alexnathanson/weathermachine/arduino-code/pumpDriver-Nov29-2022-PWM_DIR/pumpDriver-Nov29-2022-PWM_DIR.ino

/*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
 * This example shows how to drive a motor using the PWM and DIR pins.
 * This example only shows how to drive a single motor for simplicity.
 * For dual channel motor driver, both channel work the same way.
 * 
 * 
 * CONNECTIONS:
 * 
 * Arduino D3  - Motor Driver PWM Input
 * Arduino D4  - Motor Driver DIR Input
 * Arduino GND - Motor Driver GND
 *
 *
 * AUTHOR   : Kong Wai Weng
 * COMPANY  : Cytron Technologies Sdn Bhd
 * WEBSITE  : www.cytron.io
 * EMAIL    : support@cytron.io
 *
 *******************************************************************************/

 #include "CytronMotorDriver.h"


// Configure the motor driver.
CytronMD motor(PWM_DIR, 3, 4);  // PWM = Pin 3, DIR = Pin 4.


// The setup routine runs once when you press reset.
void setup() {
    motor.setSpeed(128);  // Run forward at 50% speed.

}


// The loop routine runs over and over again forever.
void loop() {
  delay(1000);
  
}
