alexnathanson/weathermachine/main/runner.py

import csv
import os
import pandas as pd
import logging
import time
from datetime import datetime
from arduinoSerial import ArduinoSerial as Arduino #this is the code for communicating with an Arduino via serial
from WeatherMachineLights import WMLights as Lights	
import math
import sys
import api
from threading import Thread
from queue import Queue
from _thread import interrupt_main
import requests
import json

dataDirectory = './data/cleaned/'

#devMode = False

#arduino = object

#import date from the file specified via the browser
def importData(dataFileName):

	# dirList = os.listdir(dataDirectory)
	fileName = dataDirectory + dataFileName

	print("importing data from " + fileName)

	try:
		with open(fileName) as csvfile:
			df = pd.read_csv(fileName)
			print(df.head())
	except IOError:
		print('failed to import ' + fileName)
		logging.exception('')
		raise SystemExit(1)
	return df

def mergeTwoColumns(c1, c2):
	return pd.merge(c1,c2,left_index=True,right_index=True)

#check if this is a float or not
def checkFloat(toCheck):

	try:
		float(toCheck)
		return True
	except ValueError:
		return False

#run through all times at specified rate
def runLoop(dF):

	dataIndex = 0

	while True:
		print('run loop')
		#get time

		#if no more data exit loop
		if dataIndex == len(dF) - 1:
			break

		dataIndex = dataIndex + 1

	print('')
	print('*** FINISHED *** ')
	print('')

#prints a progress bar on the console
#note that the terminal window needs to be wide enough to fit all text otherwise it will look wierd
def progressBar(iteration, total, prefix = 'Progress', suffix = 'Complete', suffix2 = 'Min Remaining', decimals = 1, length = 100, fill = '█', printEnd = "\r"):

    #prefix = "Progress"
	percent = ("{0:." + str(decimals) + "f}").format(100 * (iteration / float(total)))
	filledLength = int(length * iteration // total)
	bar = fill * filledLength + '-' * (length - filledLength)
	estMin = total - iteration
	print(f'\r{prefix} |{bar}| {iteration}% {suffix} {estMin} {suffix2}', end = printEnd)
	
	if iteration == 100:
		print()

'''
if tScale is a float or int it just scales the time by minutes
if tScale is a string options are:
	rt = real time running
	minute = hours converted to minutes
	seconds = hours converted to seconds
'''
def setTimeScale(tScale):
	if str(tScale).isnumeric() or checkFloat(tScale):
		print('t scale is float or int')
	elif type(tScale) == str:
		print('t scale is str')
		if tScale == 'rT':
			tScale = 1
		elif tScale == 'minute':
			tScale = 60
		elif tScale == 'seconds':
			tScale = 60 * 60
		else:
			tScale = 1

	print("new time scale: " + str(tScale))

	return tScale
	
def runLights(lData, azimuth):
	print("running lights")

	#print(lData.head())

	#instantiate the light class
	lights = Lights(azimuth)

	#print(cList)

	#create lights dataframe
	initData = {'Date Format':lData['Date Format'],'HH:MM': lData["HH:MM"]}#,lData.columns[0]:mCData
	dfLights = pd.DataFrame(initData)
	#print(dfLights.head())

	#convert the data to the proper surface
	#get the column of data we want
#	mCData = lData.iloc[:,2]
#	print(mCData.iloc[0:10])
#s	dfLights['surface conversion'] = lights.roughSurfaceOrientationConversion(mCData)

	dfLights['surface irradiance'] = lights.detailedSurfaceOrientation(lData)

	#convert from energy to lux
	dfLights['lux'] = lights.energyToLux(dfLights['surface irradiance'])

	#map lux to arduino analog range (0 to 255)
	dfLights['ard'] = lights.convertToArduinoAnalogOutput(dfLights['lux'], 120000)
	#print(dfLights.iloc[0:10])

	return dfLights

#this populates the table with consequetive dates for 1 calendar year
def normalizeDates(nDF):
	print("normalizing dates")

	daysPerMonth = [31,28,31,30,31,30,31,31,30,31,30,31]

	totDM = [0]

	#create list with cumulative total days up to that poiunt
	for d in range(1,len(daysPerMonth)):
		totDM.append(totDM[d-1] + daysPerMonth[d-1])
	
	#print(data['Date'].head())
	for i in range(len(nDF)):
		#hours in the year
		h=i+1
		#days in the year
		d = math.ceil(h/24)

		if d <= totDM[1]:
			#nDF[i] = datetime.strptime("1/" + str(d) +"/1976", '%m/%d/%Y').date()
			nDF.loc[i] = datetime.strptime("1/" + str(d) +"/1976", '%m/%d/%Y').date()
		elif d <= totDM[2]:
			nDF.iloc[i] = datetime.strptime("2/" + str(d-totDM[1]) +"/1976", '%m/%d/%Y').date()
		elif d <= totDM[3]:
			nDF.iloc[i] = datetime.strptime("3/" + str(d-totDM[2]) + "/1976", '%m/%d/%Y').date()
		elif d <= totDM[4]:
			nDF.iloc[i] = datetime.strptime("4/" + str(d-totDM[3]) + "/1976", '%m/%d/%Y').date()
		elif d <= totDM[5]:
			nDF.iloc[i] = datetime.strptime("5/" + str(d-totDM[4]) + "/1976", '%m/%d/%Y').date()
		elif d <= totDM[6]:
			nDF.iloc[i] = datetime.strptime("6/" + str(d-totDM[5]) + "/1976", '%m/%d/%Y').date()
		elif d <= totDM[7]:
			nDF.iloc[i] = datetime.strptime("7/" + str(d-totDM[6]) + "/1976", '%m/%d/%Y').date()
		elif d <= totDM[8]:
			nDF.iloc[i] = datetime.strptime("8/" + str(d-totDM[7]) + "/1976", '%m/%d/%Y').date()
		elif d <= totDM[9]:
			nDF.iloc[i] = datetime.strptime("9/" + str(d-totDM[8]) + "/1976", '%m/%d/%Y').date()
		elif d <= totDM[10]:
			nDF.iloc[i] = datetime.strptime("10/" + str(d-totDM[9]) + "/1976", '%m/%d/%Y').date()
		elif d <= totDM[11]:
			nDF.iloc[i] = datetime.strptime("11/" + str(d-totDM[10]) + "/1976", '%m/%d/%Y').date()
		else:
			nDF.iloc[i] = datetime.strptime("12/" + str(d-totDM[11]) + "/1976", '%m/%d/%Y').date()

		# if d <= totDM[1]:
		# 	data['Date'][i] = datetime.strptime("1/" + str(d) +"/1976", '%m/%d/%Y').date()
		# elif d <= totDM[2]:
		# 	data['Date'][i] = datetime.strptime("2/" + str(d-totDM[1]) +"/1976", '%m/%d/%Y').date()
		# elif d <= totDM[3]:
		# 	data['Date'][i] = datetime.strptime("3/" + str(d-totDM[2]) + "/1976", '%m/%d/%Y').date()
		# elif d <= totDM[4]:
		# 	data['Date'][i] = datetime.strptime("4/" + str(d-totDM[3]) + "/1976", '%m/%d/%Y').date()
		# elif d <= totDM[5]:
		# 	data['Date'][i] = datetime.strptime("5/" + str(d-totDM[4]) + "/1976", '%m/%d/%Y').date()
		# elif d <= totDM[6]:
		# 	data['Date'][i] = datetime.strptime("6/" + str(d-totDM[5]) + "/1976", '%m/%d/%Y').date()
		# elif d <= totDM[7]:
		# 	data['Date'][i] = datetime.strptime("7/" + str(d-totDM[6]) + "/1976", '%m/%d/%Y').date()
		# elif d <= totDM[8]:
		# 	data['Date'][i] = datetime.strptime("8/" + str(d-totDM[7]) + "/1976", '%m/%d/%Y').date()
		# elif d <= totDM[9]:
		# 	data['Date'][i] = datetime.strptime("9/" + str(d-totDM[8]) + "/1976", '%m/%d/%Y').date()
		# elif d <= totDM[10]:
		# 	data['Date'][i] = datetime.strptime("10/" + str(d-totDM[9]) + "/1976", '%m/%d/%Y').date()
		# elif d <= totDM[11]:
		# 	data['Date'][i] = datetime.strptime("11/" + str(d-totDM[10]) + "/1976", '%m/%d/%Y').date()
		# else:
		# 	data['Date'][i] = datetime.strptime("12/" + str(d-totDM[11]) + "/1976", '%m/%d/%Y').date()

	return nDF

def apiThread(outQ):
	#start API
	api.app.run()	

def runMachine():
	global arduino

	print('')
	print("*** Running Weather Machine ***")
	
	# print("wall azimuth: " + str(azimuth) + " degrees")
	# print("time scale: " + str(tScale))
	print("Arduino port: " + api.runSettings['port'])
	dataFile = api.runSettings['file'] + ".csv"
	print("Data file: " + dataFile)
	print("Facade: " + api.runSettings['facade'])

	#convert cardinal direction to azimuths
	if api.runSettings['facade'] == 'north':
		az = 0
	elif api.runSettings['facade'] == 'east':
		az = 90
	elif api.runSettings['facade'] == 'south':
		az = 180
	elif api.runSettings['facade'] == 'west':
		az = 270


		print("Time Mode: " + str(api.runSettings['time']))

	#timeMode = str(api.runSettings['time'])
	# 60 * 60 for real time
	if int(api.runSettings['time']) == 1:
		timeInc = 60 * 60
		timeMode = 'real time'
	# 60 for minute resolution 
	elif int(api.runSettings['time']) == 2:
		timeInc = 60
		timeMode = '1 hr = 1 min'
	elif int(api.runSettings['time']) == 3:
		timeInc = 1
		timeMode = '1 hr = 1 sec'
	print("Timescale: " + timeMode)

	components=''
	if api.runSettings['light'] == 'true':
		components = components + "lights "

	if components == '':
		components = 'none'

	print("Components: " + components)
	print('')

	try:
		#global arduino
		arduino = Arduino(api.runSettings['port'])
	except Exception as e:
		print(e)
		#interrupt_main()
		raise SystemExit(1)

	#rate that data is sent - currently not being used
	#tScale = setTimeScale(tScale)

	#get all the data in a dataframe
	allData = importData(dataFile)

	#normalize dates - not being used here - stop gap is in JS
	allData['Date Format'] = normalizeDates(allData['Date'])

	#format date
	#allData['Date Format'] = allData['Date'].strptime(dT, '%m/%d/%Y').date()

	#filter by day and time
	if 'sday' in api.runSettings.keys():
		print("TIME EXISTS!")
		print(api.runSettings['sday'])
		# Filter data between two dates
		timedData = allData.loc[(allData['Date Format'] >= datetime.strptime(api.runSettings['sday'], '%m-%d-%Y').date()) & (allData['Date Format'] <= datetime.strptime(api.runSettings['eday'], '%m-%d-%Y').date())]
		print(timedData.head())

	###### LIGHTS ######
	if api.runSettings['light'] == 'true':
		# columns needed for light calculations:
		lightCols = ['Date Format', 'HH:MM', 'Global Horizontal Radiation {Wh/m2}','Direct Normal Radiation {Wh/m2}','Diffuse Horizontal Radiation {Wh/m2}']
		dfLights = runLights(timedData[lightCols], az)
		print(dfLights.head())

	print("Output:")

	startTime = datetime.now()

	stats = {"percent":0,"elapsedTime":0,"estimatedRemainingTime":0,"light":0}

	dFLen = len(dfLights)

	#convert df to json for POSTing
	jsonLights = {}
	for i in range(dFLen):
		#jsonLights[dfLights['Date Format'][i].strftime("%Y-%m-%d") + " " + dfLights['HH:MM'][i]] = int(dfLights['ard'][i])
		jsonLights[dfLights['Date Format'][i].strftime("%Y-%m-%d") + " " + dfLights['HH:MM'][i]] = int(dfLights['ard'][i])

	#print(jsonLights)
	postToAPI('data', json.dumps(jsonLights))

	#this runs if 1 hour is transposed to roughly 1 second (each value is sent every second)
	if api.runSettings['time'] == 3:
		for i in range(dFLen):
			if api.runIt == False:
				arduino.turnOff()
				arduino.serialObj.close()
				break
			elif api.runIt == True:

				lB = dfLights['ard'][i]
				#print("Sending: " + str(lB))
				arduino.sendByte(str(lB).encode())

				#run stats
				stats['percent'] = 100 * float((i+1) / dFLen)
				stats['elapsedTime'] = int((datetime.now() - startTime).total_seconds())
				stats['estimatedRemainingTime'] = (stats['elapsedTime'] / stats['percent']) * (100 - stats['percent'])
				stats['light'] = int(lB)
				# if len(stats['light']) <= 0:
				# 	stats['light'] = [lB]
				# else:
				# 	#stats['light']=
				# 	stats['light'].append(lB)
				#print(str(round(stats['percent'],3)) + "% - " + str(stats['elapsedTime']) + " seconds - " + str(stats['estimatedRemainingTime']) + " seconds")

				# url = 'http://localhost:5000/runStats'
				# headers = {'Content-type': 'application/json', 'Accept': 'text/plain'}
				# x = requests.post(url, data=json.dumps(stats), headers=headers)

				postToAPI('runStats', stats)

			 	#this is in seconds
				time.sleep(1)
	#smooth values between hourly values
	else:
		while True:
			if api.runIt == False:
				arduino.turnOff()
				arduino.serialObj.close()
				break
			elif api.runIt == True:
				#run stats
				stats['elapsedTime'] = int((datetime.now() - startTime).total_seconds())

				#determine how many hours have elapsed
				#the max number sent out should not exceed to the total amount of hours in the data

				eHours = math.floor(min(math.floor(stats['elapsedTime'] / timeInc),dFLen-1))

				stats['percent'] = 100 * float((eHours+1) / dFLen)
				stats['estimatedRemainingTime'] = (stats['elapsedTime'] / stats['percent']) * (100 - stats['percent'])

				print(eHours)

				if eHours < dFLen-1:
					timeMidPoint = stats['elapsedTime'] / timeInc - math.floor(stats['elapsedTime'] / timeInc)
					print(timeMidPoint)
					stats['light'] = abs(dfLights['ard'][eHours] - (dfLights['ard'][eHours]+1)) * timeMidPoint
					#lB = dfLights['ard'][eHours]
					#print("Sending: " + str(lB))
					arduino.sendByte(str(stats['light']).encode())
				
					postToAPI('runStats', stats)
				elif eHours == dFLen-1:
					stats['light'] = dfLights['ard'][eHours]
					#print("Sending: " + str(lB))
					arduino.sendByte(str(stats['light']).encode())
				
					postToAPI('runStats', stats)

					break

			 	#this is in seconds
				time.sleep(2)

	api.runIt = False

def postToAPI(endPoint,pData):
	url = 'http://localhost:5000/' + endPoint
	headers = {'Content-type': 'application/json', 'Accept': 'text/plain'}
	x = requests.post(url, data=json.dumps(pData), headers=headers)

def runAll():

	#Object that signals shutdown
	_sentinel = object()

	q = Queue()
	t1 = Thread(target = apiThread, args =(q, ), daemon = True)
	t1.start()

	try:
		while True:
			if api.runIt == True:
				runMachine()
			time.sleep(3)
	except KeyboardInterrupt:
		#t1.join()
		print("Keyboard Interrupt Exception")

		#turn off the arduino outputs if possible
		try:
			arduino.turnOff()
		except:
			pass
		raise SystemExit(1)

if __name__ == '__main__':
	runAll()
