alexnathanson/weathermachine/main/arduinoSerial.py

import serial
import time
from threading import Thread
from queue import Queue
from _thread import interrupt_main

class ArduinoSerial():
    def __init__(self, aPort):
        self.port = aPort
        self.baud = 9600
        if self.port != 'DEVMODE':
            self.serialObj = serial.Serial(self.port, self.baud) #might want to add timeout , timeout=0.1
            print("Arduino Serial connection starting...")
            time.sleep(3)
            #the below 2 lines were commented in originally and need to be tested
            #self.receivedString = self.serialObj.readline()
            #print(self.receivedString.decode("utf-8") )
            self.devmode = False
            self.serialData = ''
            self.readThread = Thread(target = self.readSerial, daemon = True)
            self.readThread.start()
        else:
            self.devmode = True
            print("Running in DEVMODE with no Arduino")

#arduino = serial.Serial(port='COM4', baudrate=115200, timeout=.1)

# def write_read(x):
#     arduino.write(bytes(x, 'utf-8'))
#     time.sleep(0.05)
#     data = arduino.readline()
#     return data

# while True:
#     num = input("Enter a number: ") # Taking input from user
#     value = write_read(num)
#     print(value) # printing the value
    
    #this function attempts to shut down all the subsystems properly before closing the program
    def turnOff(self):
        if not self.devmode:
            print('Attempting to shut off subsystems before exit')
            self.readThread.join()
            self.serialObj.write(str(0).encode()) 

    def sendByte(self,theByte):
        #with serial.Serial(self.port, self.baud, timeout=1) as ser:
            #time.sleep(0.5)
        print("byte: " + str(theByte))
        if not self.devmode:
            self.serialObj.write(theByte)   # send the pyte string 'H'
            #time.sleep(0.5)   # wait 0.5 seconds
            #ser.write(b'L')   # send the byte string 'L'

    def readSerial(self):
        #ser = serial.Serial(comport, baudrate, timeout=0.1)         # 1/timeout is the frequency at which the port is read
        print('running read serial')
        while True:
            newS = False
            while self.serialObj.in_waiting:
                newS = True
                self.serialData = self.serialObj.readline().decode('utf-8')
            if newS:
                print(self.serialData)
                newS = False

            #self.receivedString = self.serialObj.readline()
            #print(self.receivedString.decode("utf-8") )

    # def readSerialThread():
    #     #Object that signals shutdown
    #     _sentinel = object()

    #     q = Queue()
    #     readT = Thread(target = self.readSerial, args =(q, ), daemon = True)
    #     readT.start()
